sergiopolog/tlcs90-rom-reader/img/mcu-mo91028.jpeg

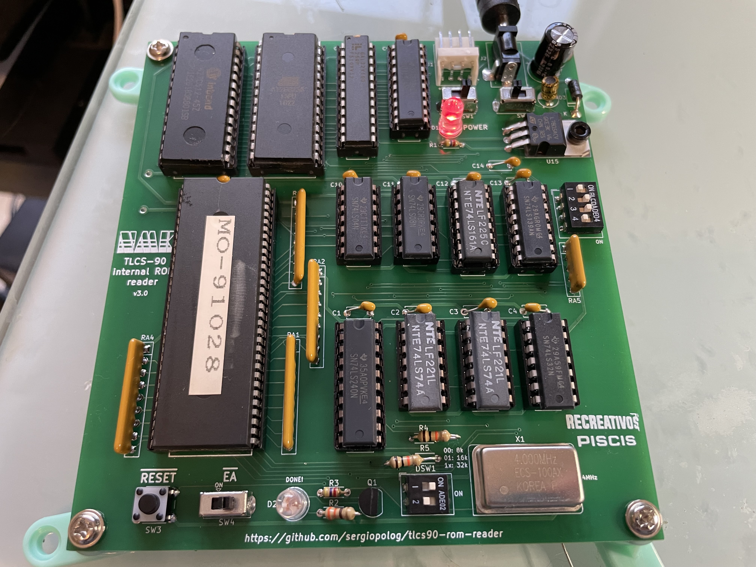
img/mcu-mo91028.jpeg
