sergiopolog/tlcs90-rom-reader/img/mcu-nmk004.jpeg

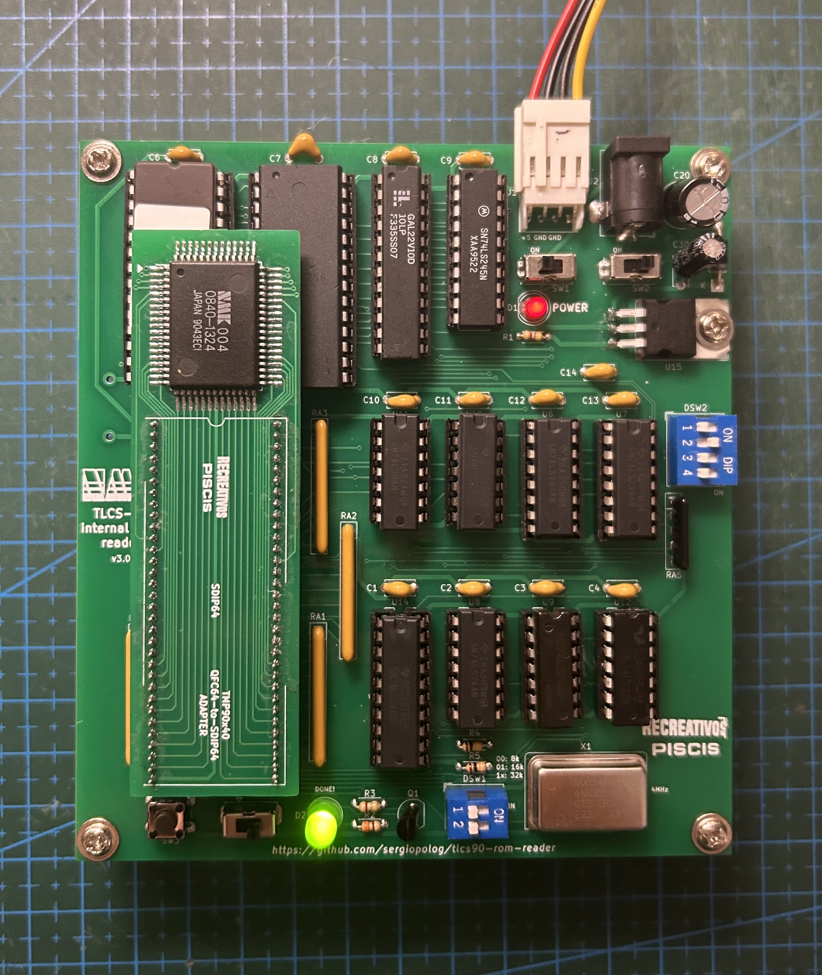
img/mcu-nmk004.jpeg
