sergiopolog/tlcs90-rom-reader/img/TLCS90-rom-reader-v1-fixing.jpg

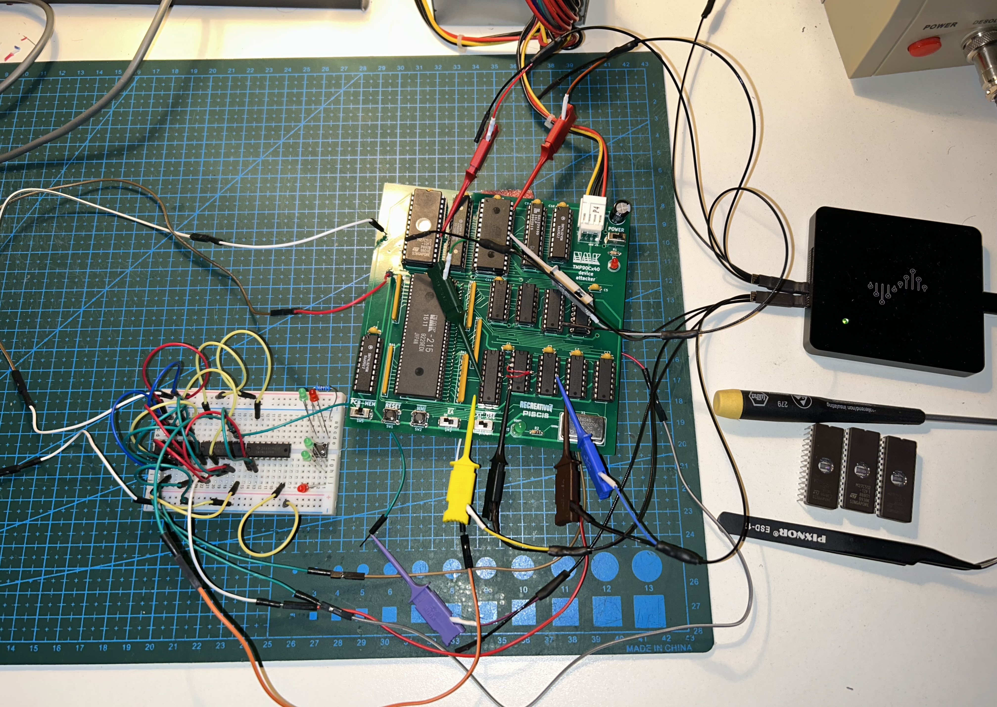
img/TLCS90-rom-reader-v1-fixing.jpg
