sergiopolog/tlcs90-rom-reader/img/TLCS90-rom-reader-v2-analyzing.jpg

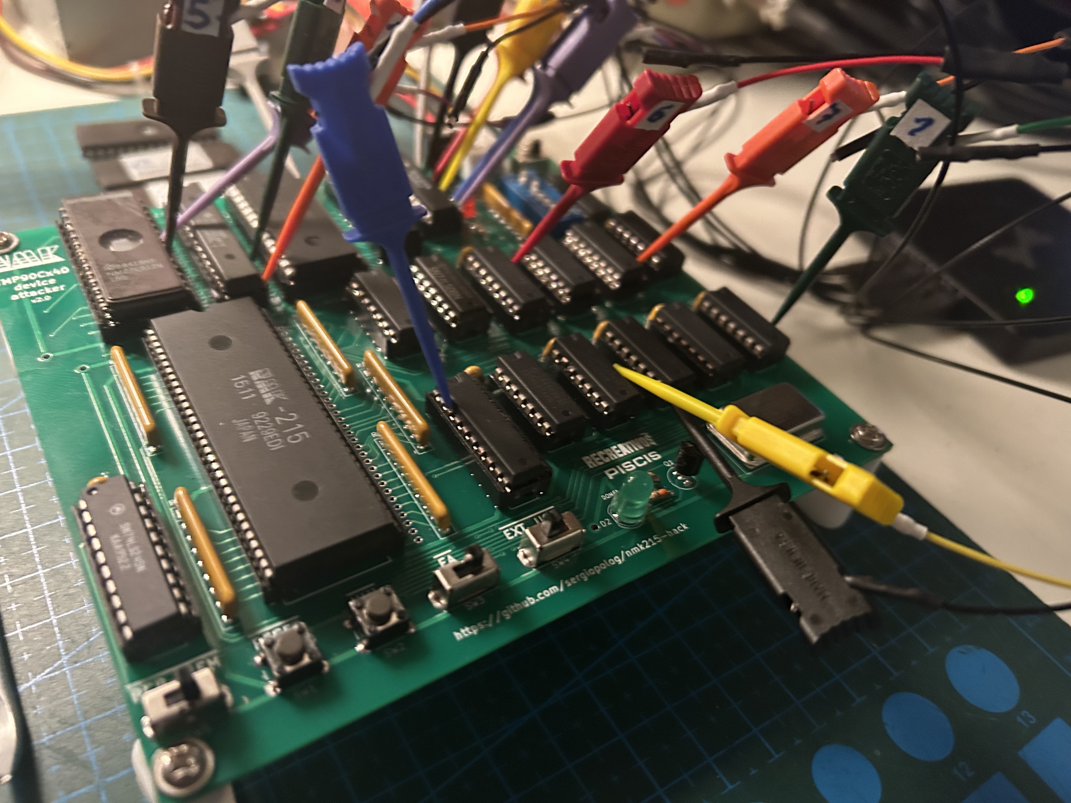
img/TLCS90-rom-reader-v2-analyzing.jpg
