sergiopolog/tlcs90-rom-reader/img/TLCS90-rom-reader-v2-fixing.jpg

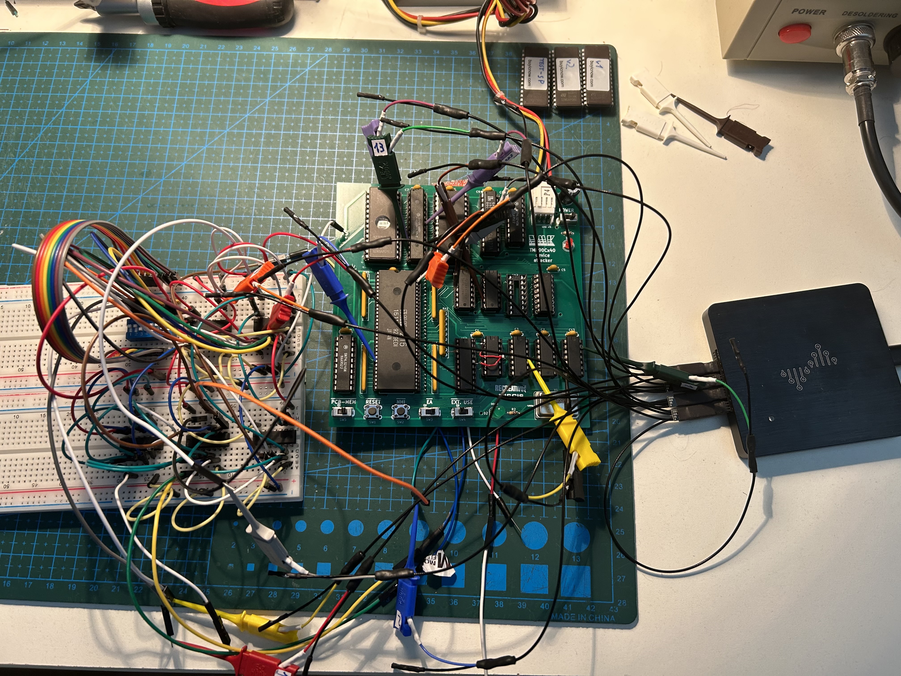
img/TLCS90-rom-reader-v2-fixing.jpg
