sergiopolog/tlcs90-rom-reader/img/mcu-cafebrk.jpeg

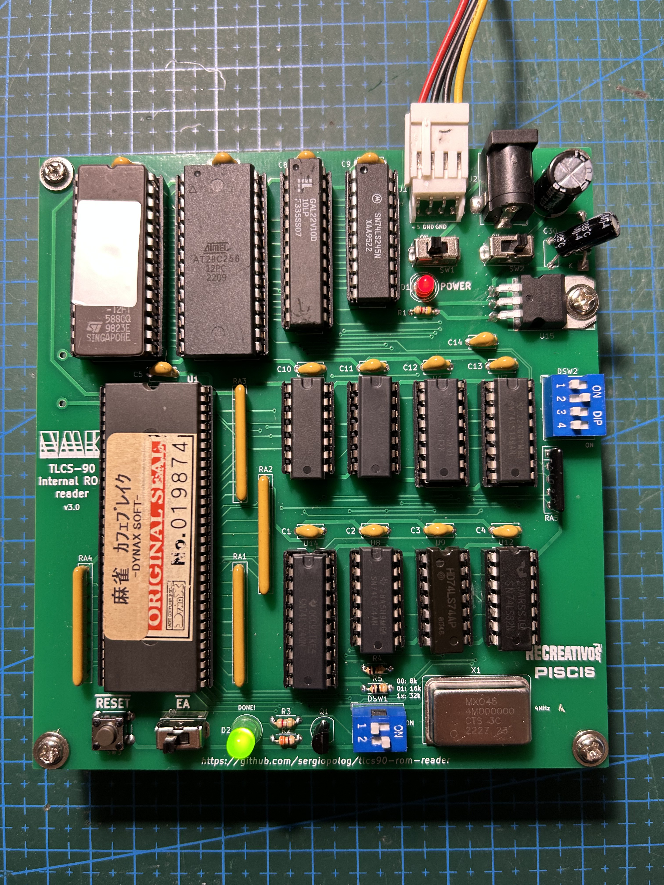
img/mcu-cafebrk.jpeg
