sergiopolog/tlcs90-rom-reader/img/mcu-cafedoll.jpeg

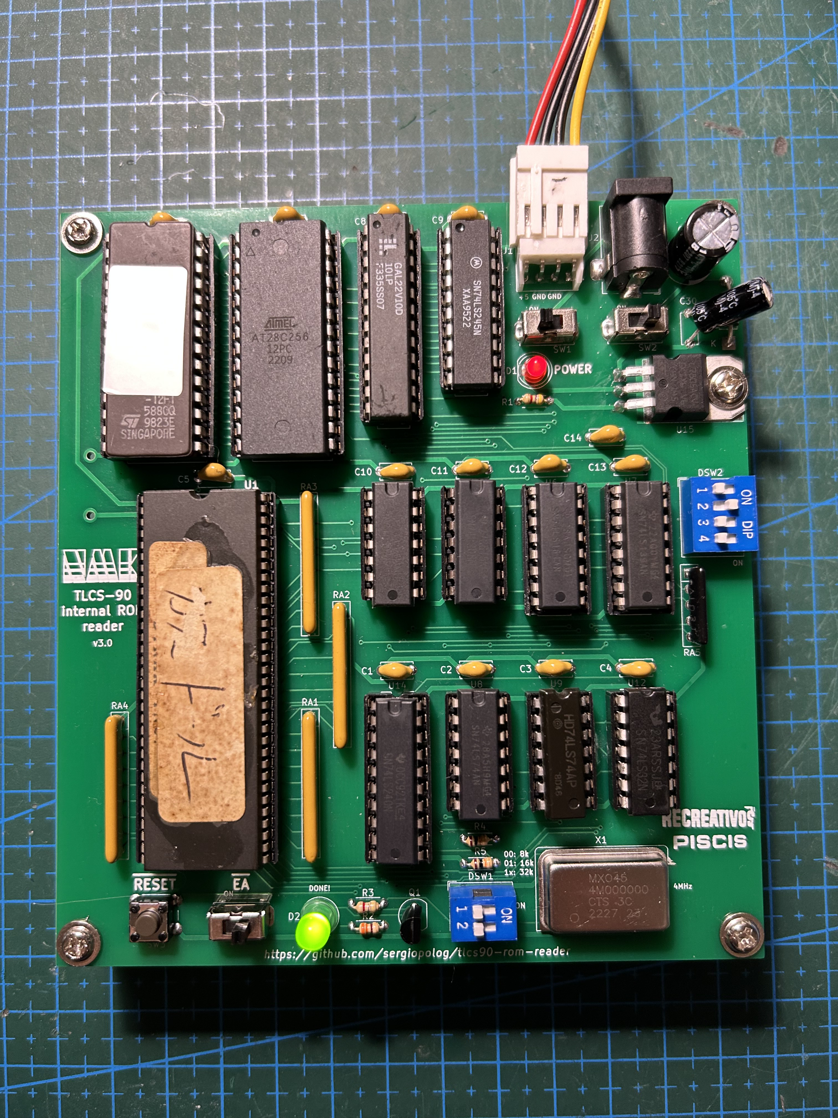
img/mcu-cafedoll.jpeg
