sergiopolog/tlcs90-rom-reader/img/mcu-edf.jpeg

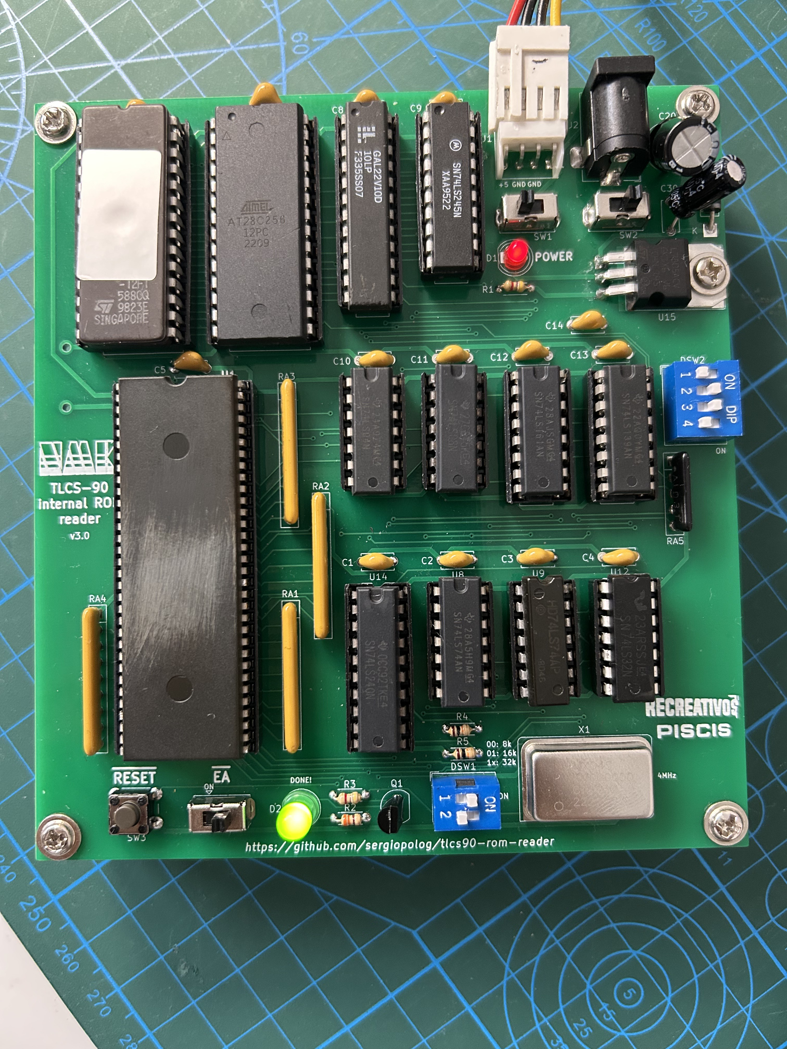
img/mcu-edf.jpeg
