sergiopolog/tlcs90-rom-reader/img/mcu-majrjhdx.jpeg

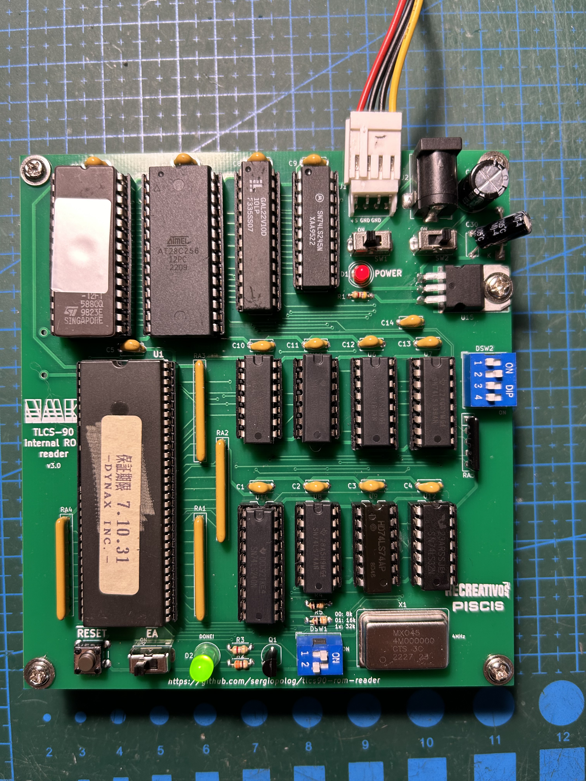
img/mcu-majrjhdx.jpeg
