sergiopolog/tlcs90-rom-reader/img/mcu-mjvegas.jpeg

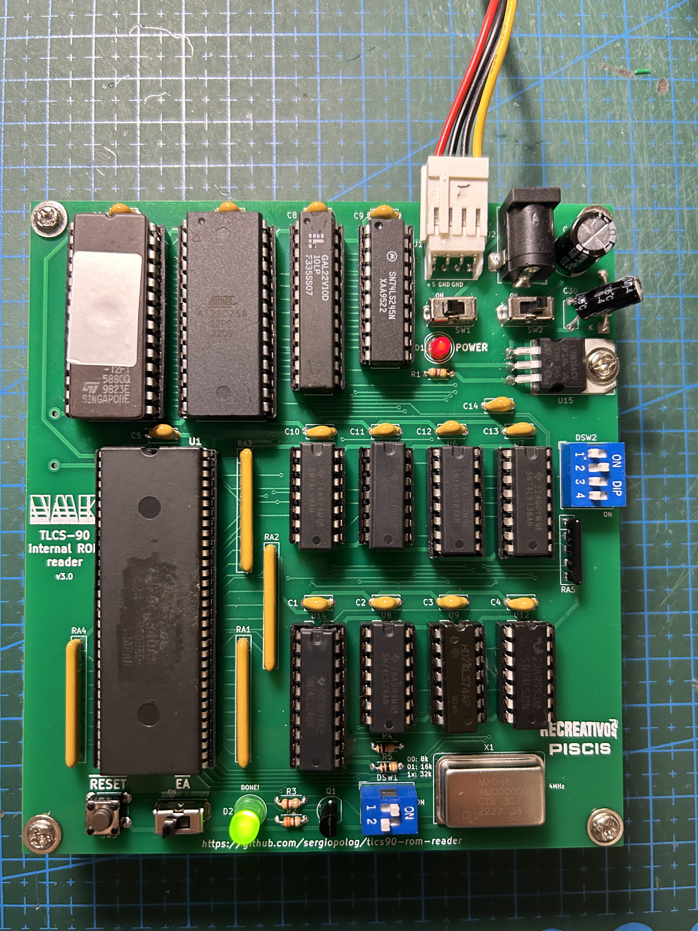
img/mcu-mjvegas.jpeg
