sergiopolog/tlcs90-rom-reader/img/mcu-mo91009.jpeg

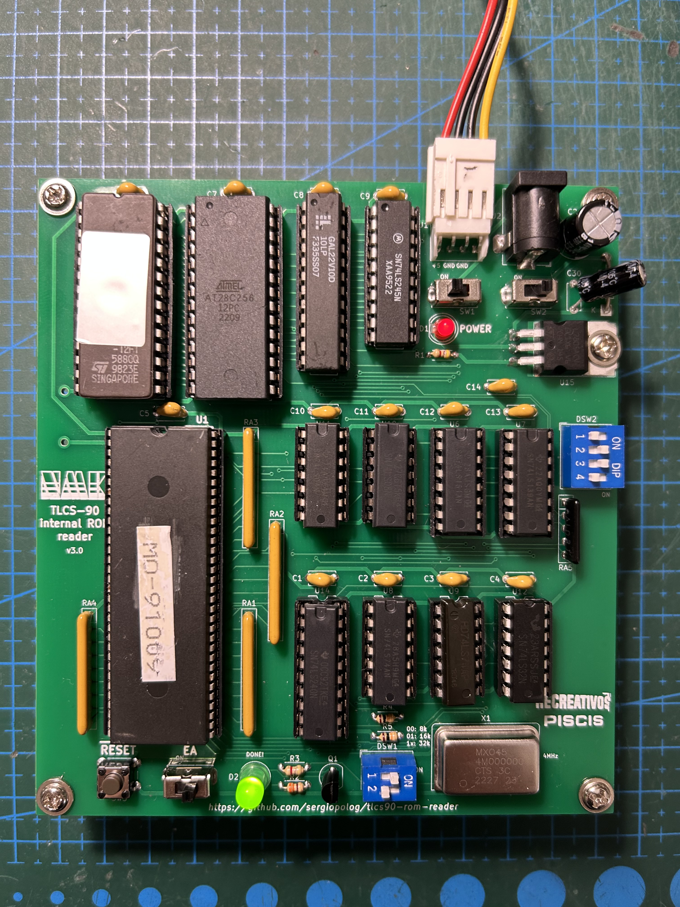
img/mcu-mo91009.jpeg
