sergiopolog/tlcs90-rom-reader/img/mcu-mo91021.jpeg

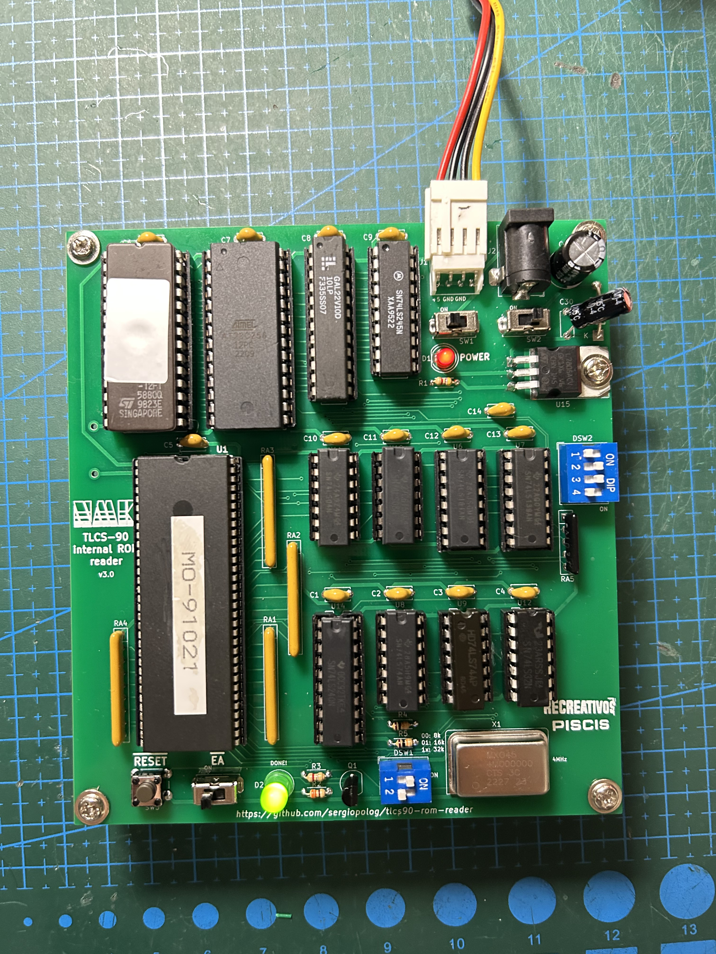
img/mcu-mo91021.jpeg
