sergiopolog/tlcs90-rom-reader/img/mcu-mo92033.jpeg

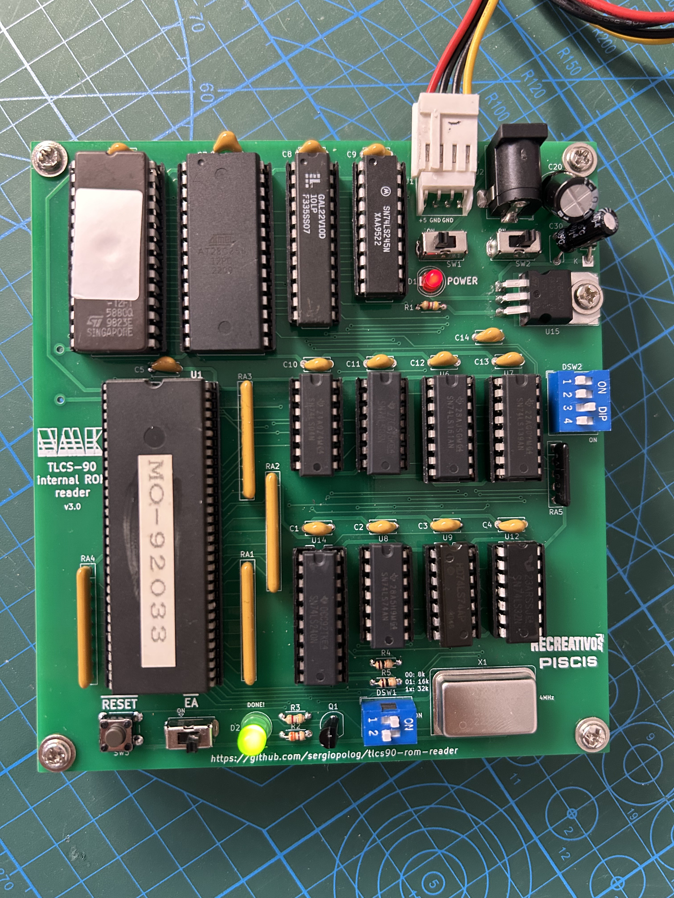
img/mcu-mo92033.jpeg
