sergiopolog/tlcs90-rom-reader/img/mcu-nmk110.jpeg

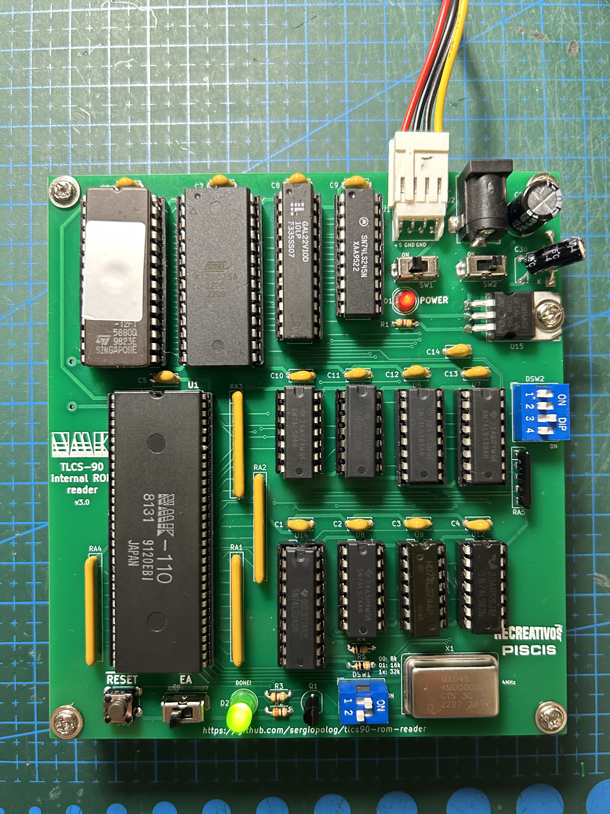
img/mcu-nmk110.jpeg
