sergiopolog/tlcs90-rom-reader/img/mcu-nmk113.jpeg

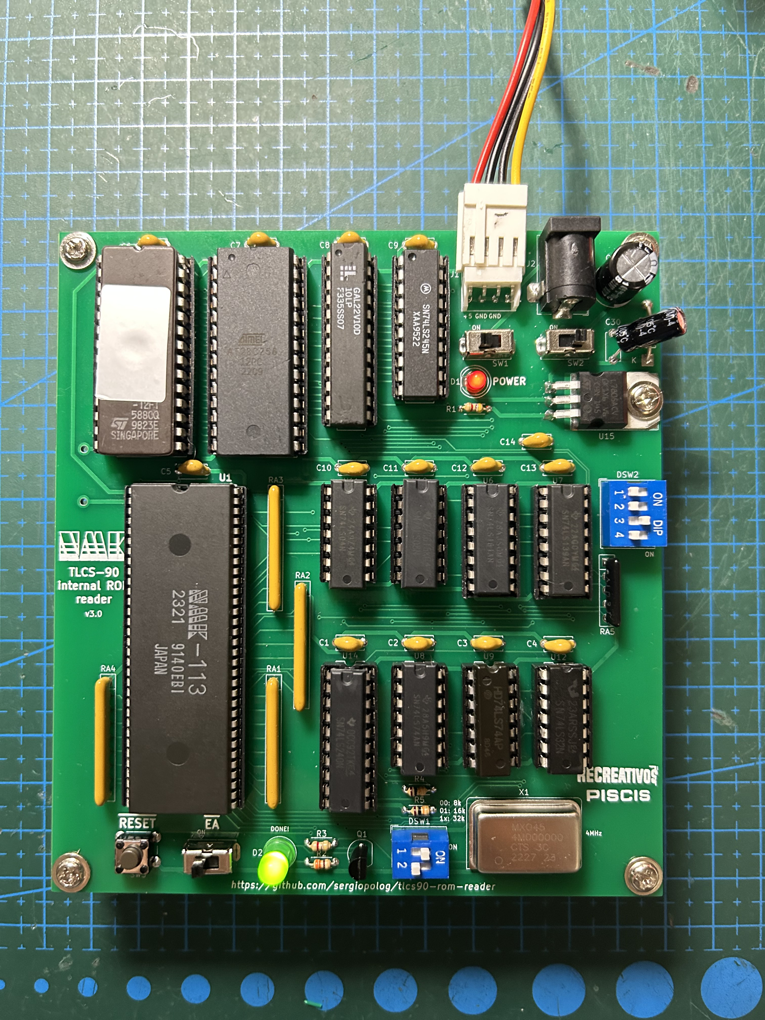
img/mcu-nmk113.jpeg
