sergiopolog/tlcs90-rom-reader/img/mcu-ougonhai.jpeg

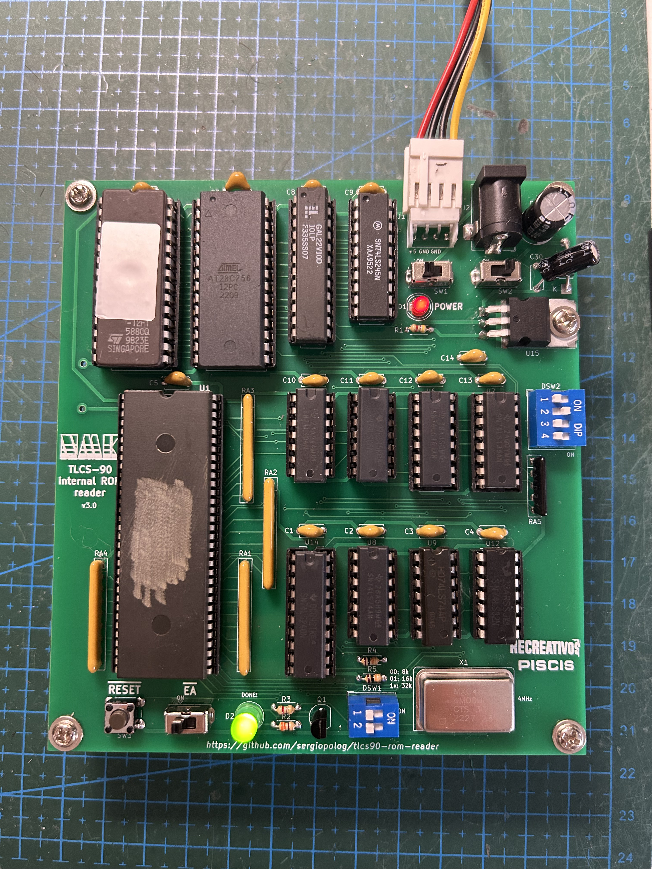
img/mcu-ougonhai.jpeg
