sergiopolog/tlcs90-rom-reader/img/mcu-t1600psu.jpeg

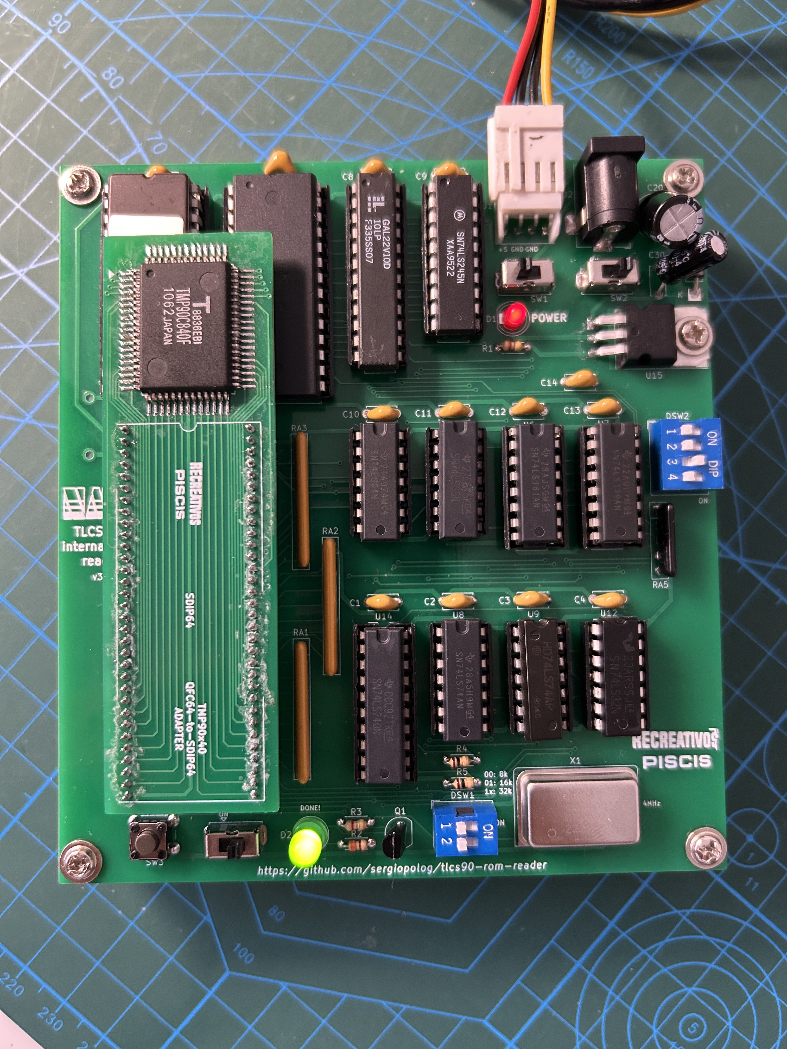
img/mcu-t1600psu.jpeg
